Midlandswim/ORCA/Media/RandomProgressPics/3DView.png

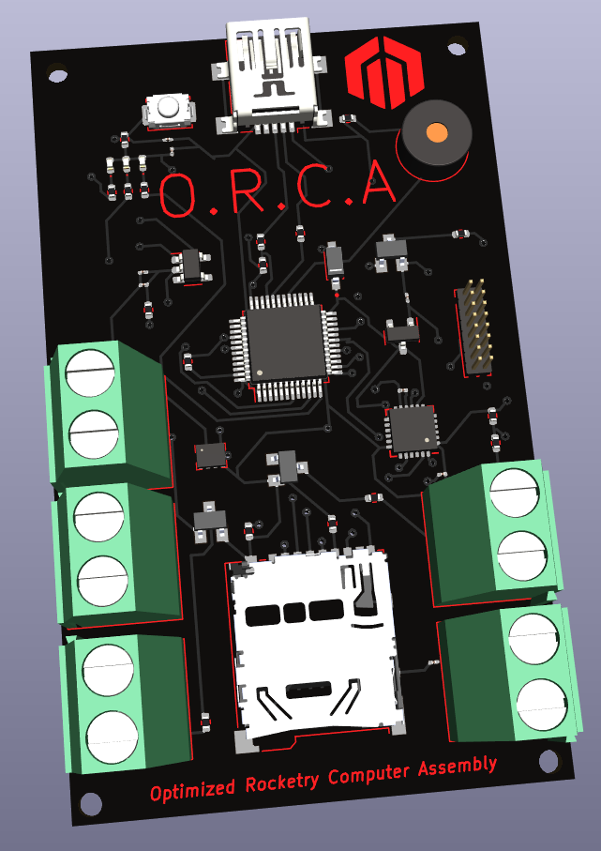
Media/RandomProgressPics/3DView.png
