Midlandswim/ORCA/Media/RandomProgressPics/3.0BoardDimensionalAnalysis(ChangesLater).png

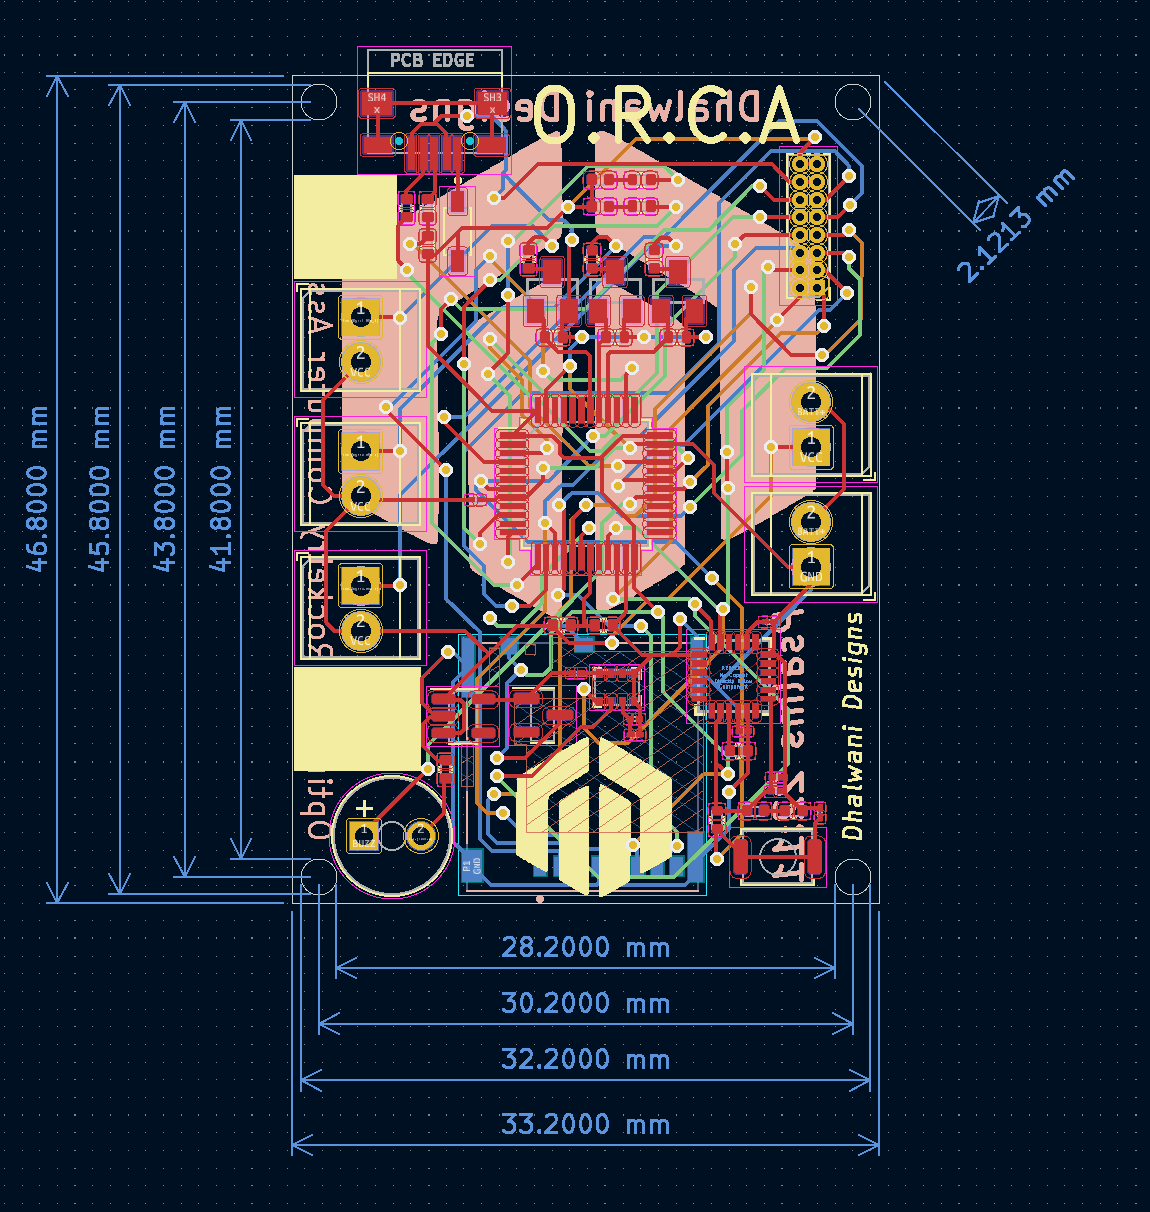
Media/RandomProgressPics/3.0BoardDimensionalAnalysis(ChangesLater).png
